koogar/Tick-Tach-Watch-Timergrapher/Solidworks/TML_TickTacho_Timergraph_Mic_SWModel/PCB_50x70_2,54.stp

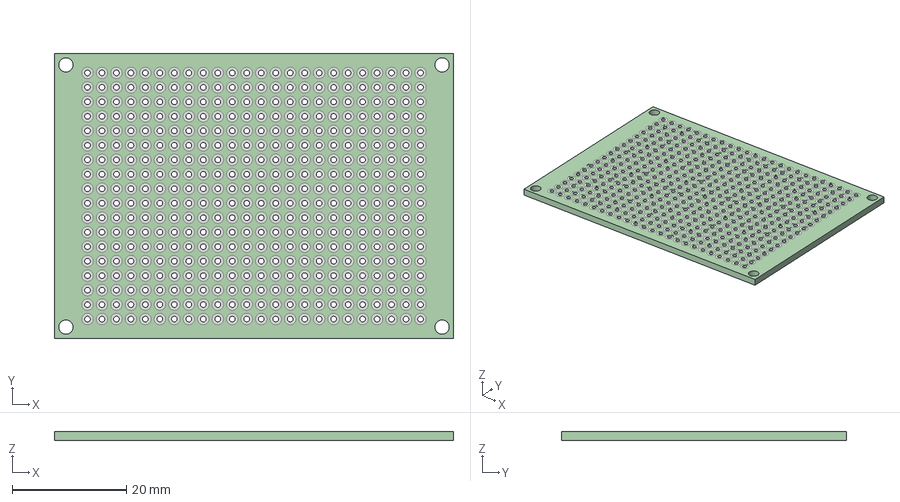
[picture p27: CAD file, 2025-09-05]
Solidworks/TML_TickTacho_Timergraph_Mic_SWModel/PCB_50x70_2,54.stp
70.0 x 50.0 x 1.60 mm
