koogar/Tick-Tach-Watch-Timergrapher/Solidworks/TML_TickTacho_Timergraph_Mic_SWModel/Proto_PCB_TickTach_2,54.SLDPRT

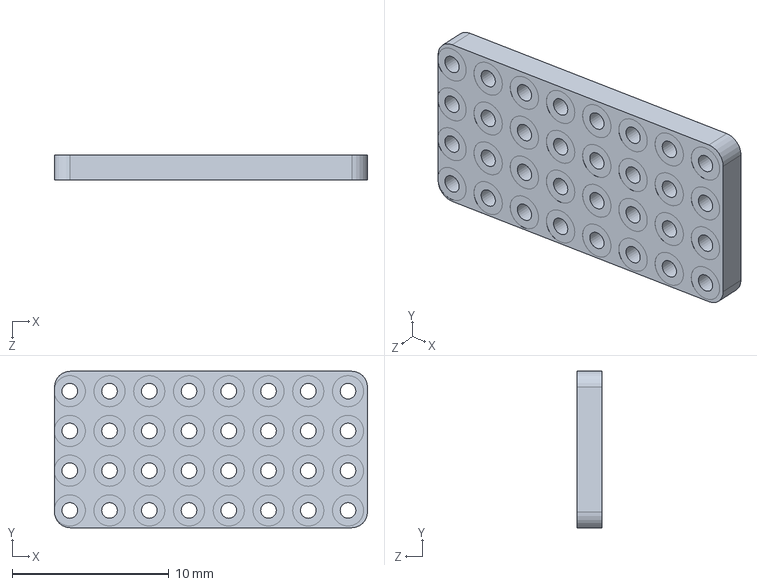
[picture p28: CAD file, 2025-09-05]
Solidworks/TML_TickTacho_Timergraph_Mic_SWModel/Proto_PCB_TickTach_2,54.SLDPRT
20.0 x 10.0 x 1.60 mm
