koogar/Tick-Tach-Watch-Timergrapher/Solidworks/TML_TickTacho_Timergraph_Mic_SWModel/Dip Switch.SLDPRT

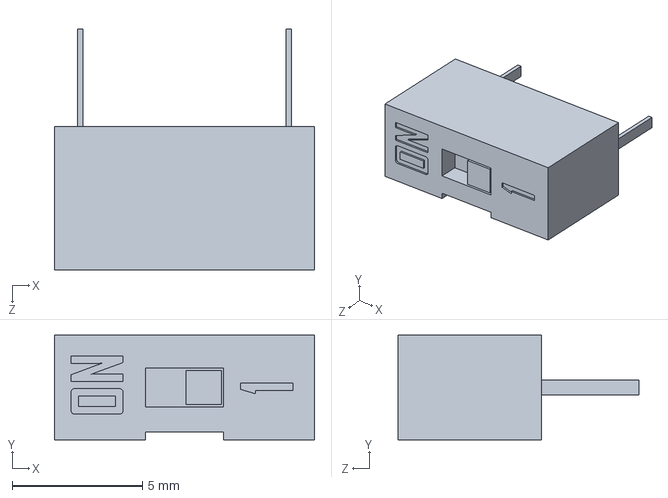
[picture p29: CAD file, 2025-09-05]
Solidworks/TML_TickTacho_Timergraph_Mic_SWModel/Dip Switch.SLDPRT
9.97 x 4.02 x 9.25 mm
