koogar/Tick-Tach-Watch-Timergrapher/Solidworks/TML_TickTacho_Timergraph_Mic_SWModel/TML_TickTacho_Timergraph_Mic_Bobble_14mm_V2.1.SLDASM

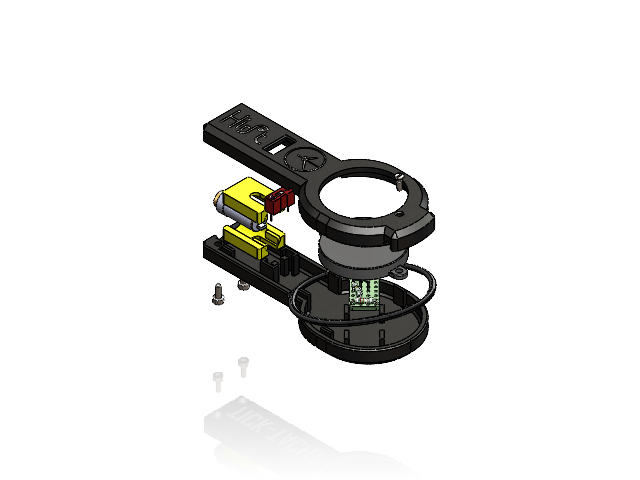
[picture p30: CAD file, 2025-09-05]
Solidworks/TML_TickTacho_Timergraph_Mic_SWModel/TML_TickTacho_Timergraph_Mic_Bobble_14mm_V2.1.SLDASM
TML_TickTacho_Timergraph_Mic_TopCover v2.1
30mm Piezo
Audio Jack
Dip Switch
TML_TickTacho_Timergraph_Mic_BottomCover v2.1
flat countersunk head tapping screw_am
Bobble
socket head cap screw_am x 2
Proto_PCB_TickTach_2,54
Resistor x 2
2N2222.step
2N2222 horizontal.step
Jack Housing Bottom x 2
